Szymon423/Christmass-Tree/Hardware/KiCad/Assets/bauble.png

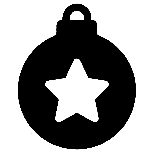
Hardware/KiCad/Assets/bauble.png
