Szymon423/Christmass-Tree/Hardware/KiCad/Assets/candy.png

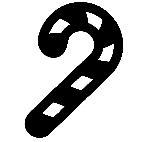
Hardware/KiCad/Assets/candy.png
