Szymon423/Christmass-Tree/Hardware/KiCad/Assets/cookie.png

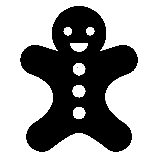
Hardware/KiCad/Assets/cookie.png
