Szymon423/Christmass-Tree/Hardware/KiCad/Assets/gift.png

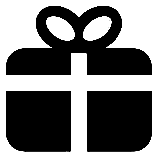
Hardware/KiCad/Assets/gift.png
