Szymon423/Christmass-Tree/Hardware/KiCad/Assets/snowflake2.png

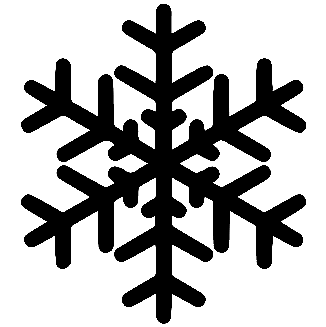
Hardware/KiCad/Assets/snowflake2.png
