Szymon423/Christmass-Tree/Hardware/KiCad/Assets/snowflake3.png

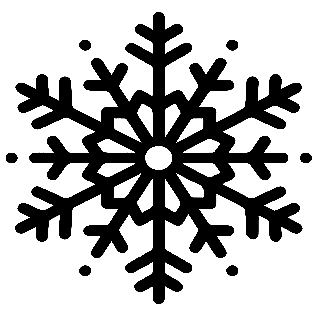
Hardware/KiCad/Assets/snowflake3.png
