Szymon423/Christmass-Tree/Hardware/KiCad/Assets/star2.png

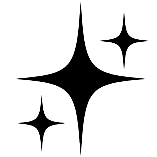
Hardware/KiCad/Assets/star2.png
