Szymon423/Christmass-Tree/Hardware/KiCad/Assets/star4.png

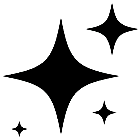
Hardware/KiCad/Assets/star4.png
