Szymon423/Christmass-Tree/Hardware/KiCad/Assets/star5.png

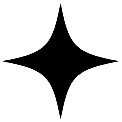
Hardware/KiCad/Assets/star5.png
