Szymon423/Christmass-Tree/Hardware/KiCad/Assets/Top-View.png

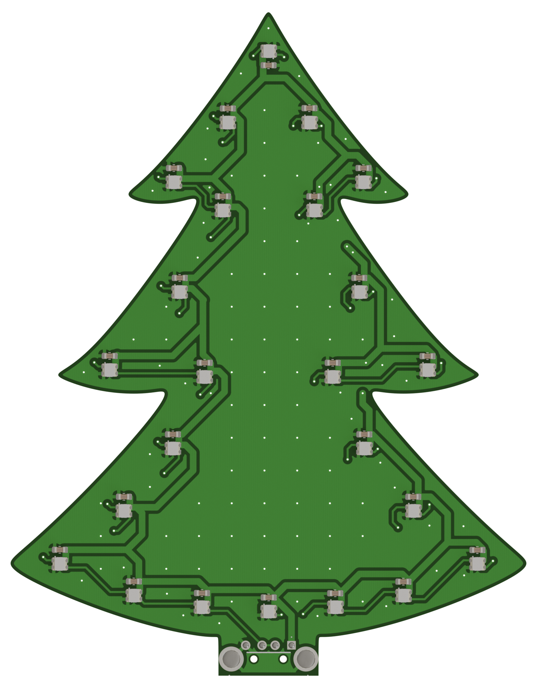
Hardware/KiCad/Assets/Top-View.png
